NewCalBoy/Projet_Gaia_Runner/media/picture/HC_05_pin_outc.webp

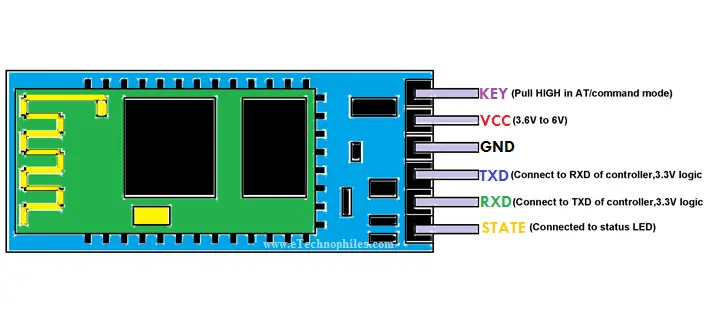
media/picture/HC_05_pin_outc.webp
