NewCalBoy/Projet_Gaia_Runner/media/picture/Module_Bluetooth_HC05.jpg

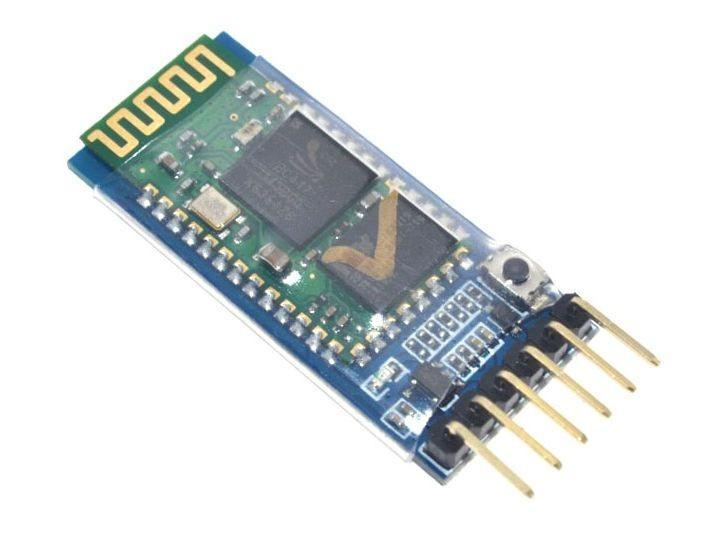
media/picture/Module_Bluetooth_HC05.jpg
